brkrot/AlsHelper/Documents/צילומי מסך אפליקציה/מסך בחירת החיישנים.jpg

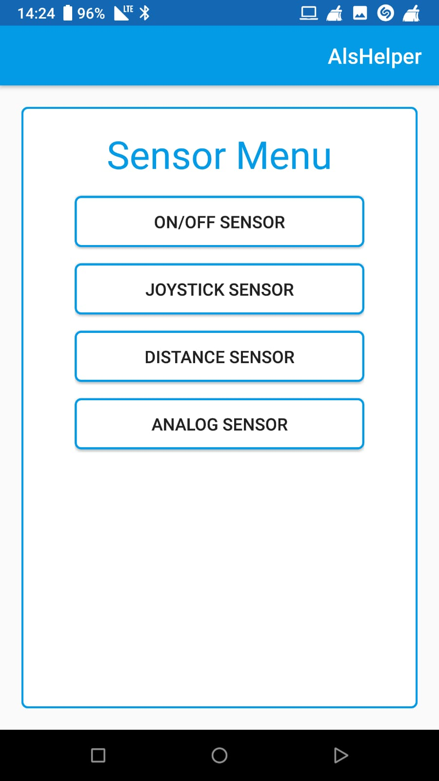
Documents/צילומי מסך אפליקציה/מסך בחירת החיישנים.jpg
