brkrot/AlsHelper/Documents/צילומי מסך אפליקציה/מסך שיתוף קוד אישי.jpg

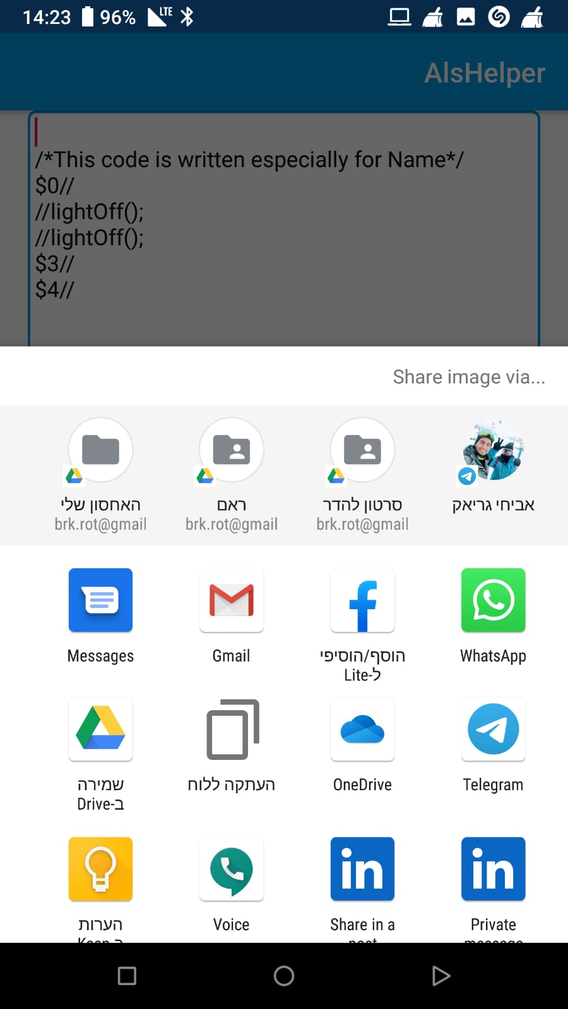
Documents/צילומי מסך אפליקציה/מסך שיתוף קוד אישי.jpg
