brkrot/AlsHelper/Documents/צילומי מסך אפליקציה/מסך תקשורת עזר 1.jpg

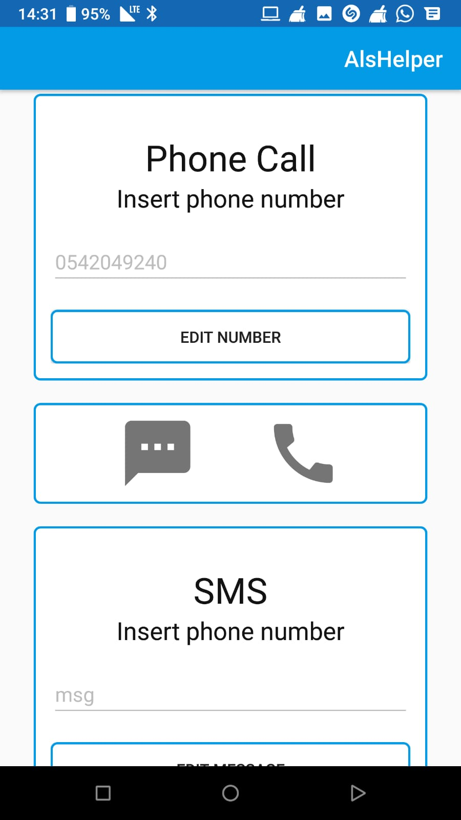
Documents/צילומי מסך אפליקציה/מסך תקשורת עזר 1.jpg
