brkrot/AlsHelper/Documents/צילומי מסך אפליקציה/מסך תקשורת עזר 2.jpg

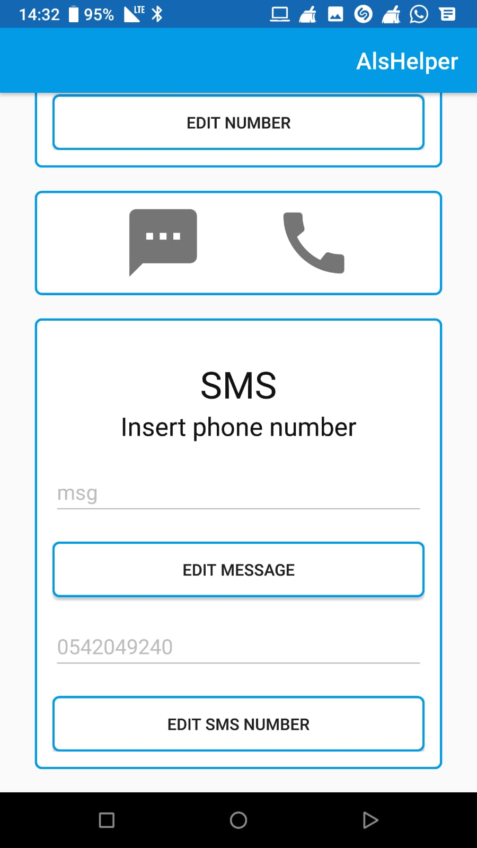
Documents/צילומי מסך אפליקציה/מסך תקשורת עזר 2.jpg
