brkrot/AlsHelper/Documents/צילומי מערכת/חיישן כפתור לחיצה רכה.jpeg

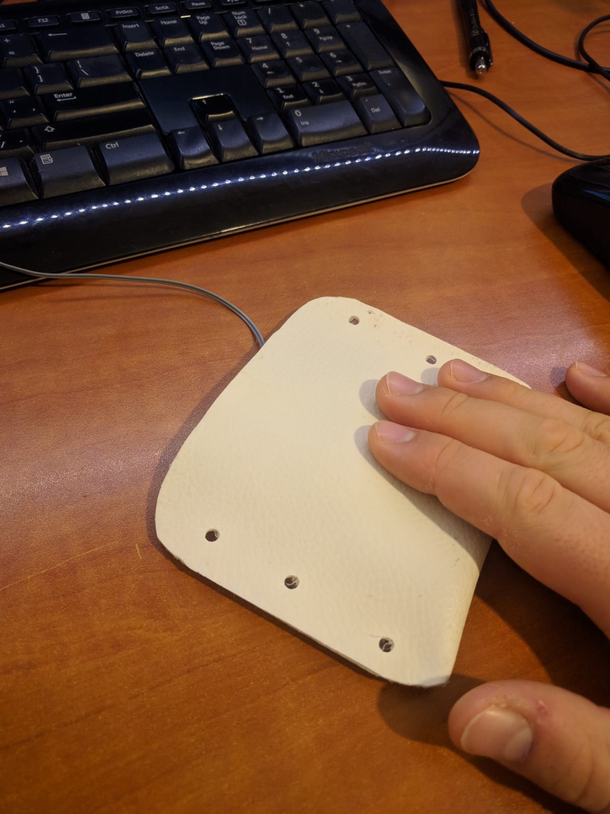
Documents/צילומי מערכת/חיישן כפתור לחיצה רכה.jpeg
