brkrot/AlsHelper/Documents/צילומי מערכת/מערכת עזר מבט חיצוני כולל.jpeg

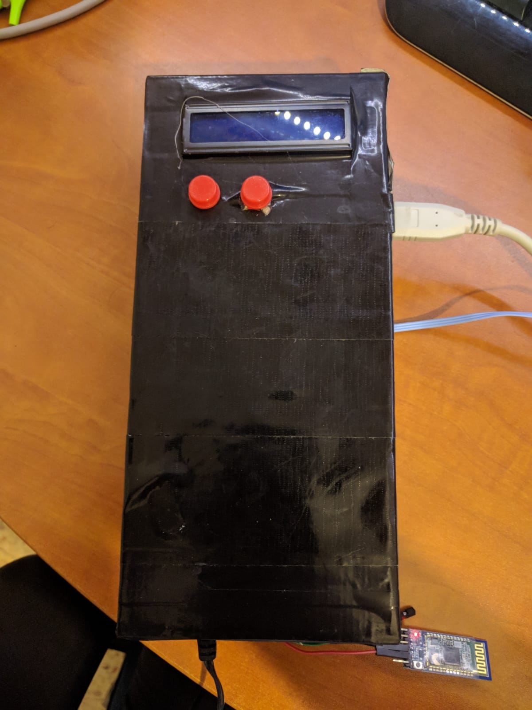
Documents/צילומי מערכת/מערכת עזר מבט חיצוני כולל.jpeg
