brkrot/AlsHelper/Documents/צילומי מערכת/מערכת עזר מבט חיצוני על המסך.jpeg

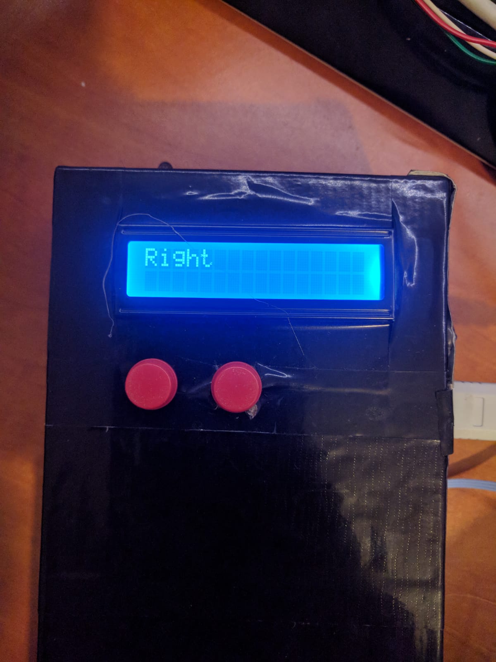
Documents/צילומי מערכת/מערכת עזר מבט חיצוני על המסך.jpeg
