brkrot/AlsHelper/Documents/צילומי מערכת/מערכת עזר פנימי.jpg

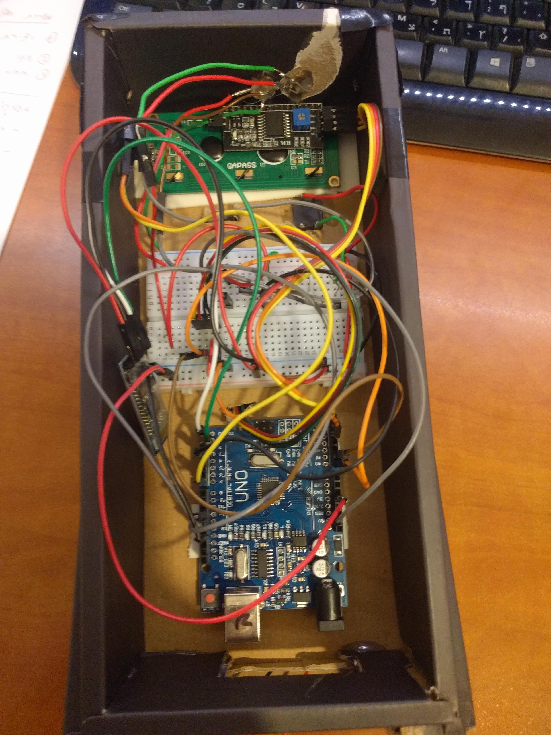
Documents/צילומי מערכת/מערכת עזר פנימי.jpg
