brkrot/AlsHelper/Documents/תרשימים/Helping_System_Sketch_2.0_bb.png

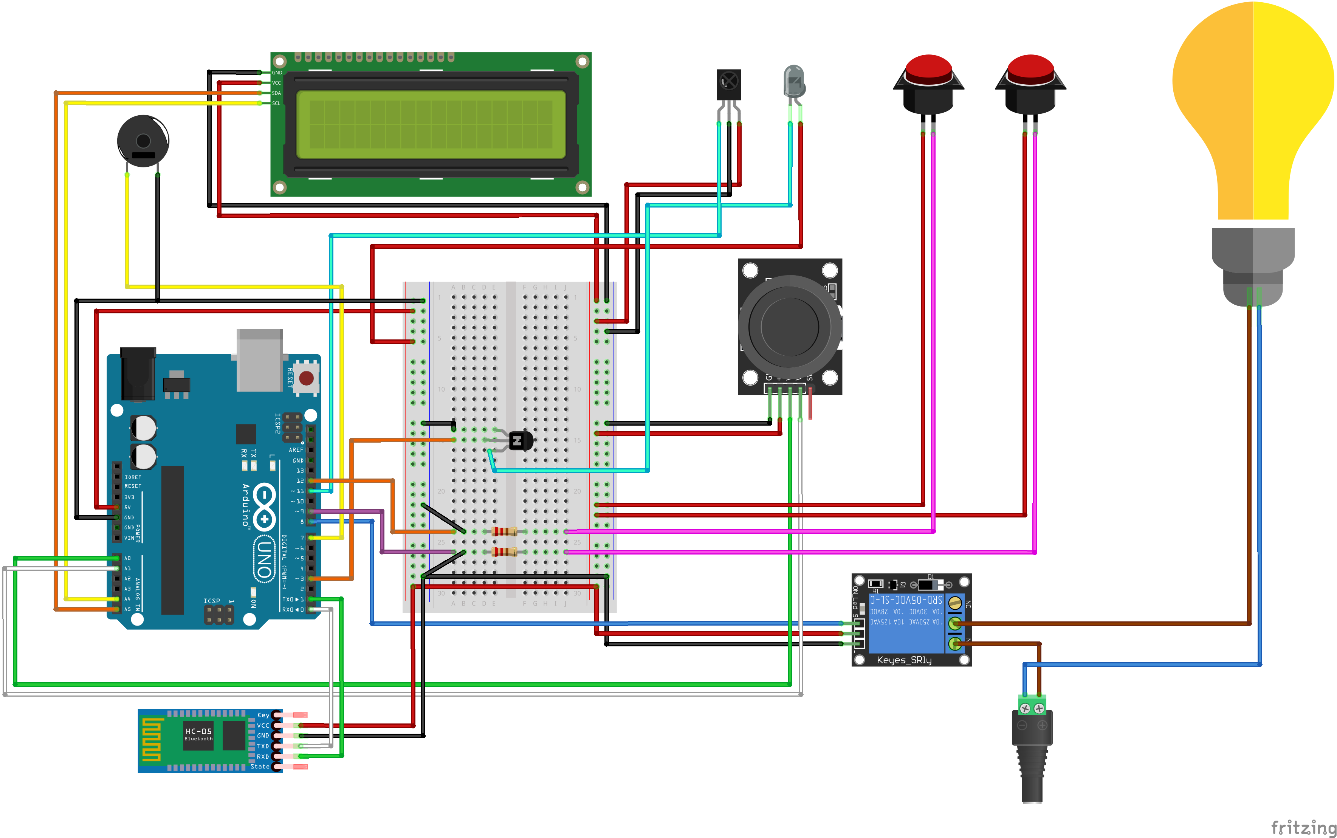
Documents/תרשימים/Helping_System_Sketch_2.0_bb.png
