brkrot/AlsHelper/Documents/תרשימים/IR_Reciever_Transmitter_Sketch_1.0_bb.png

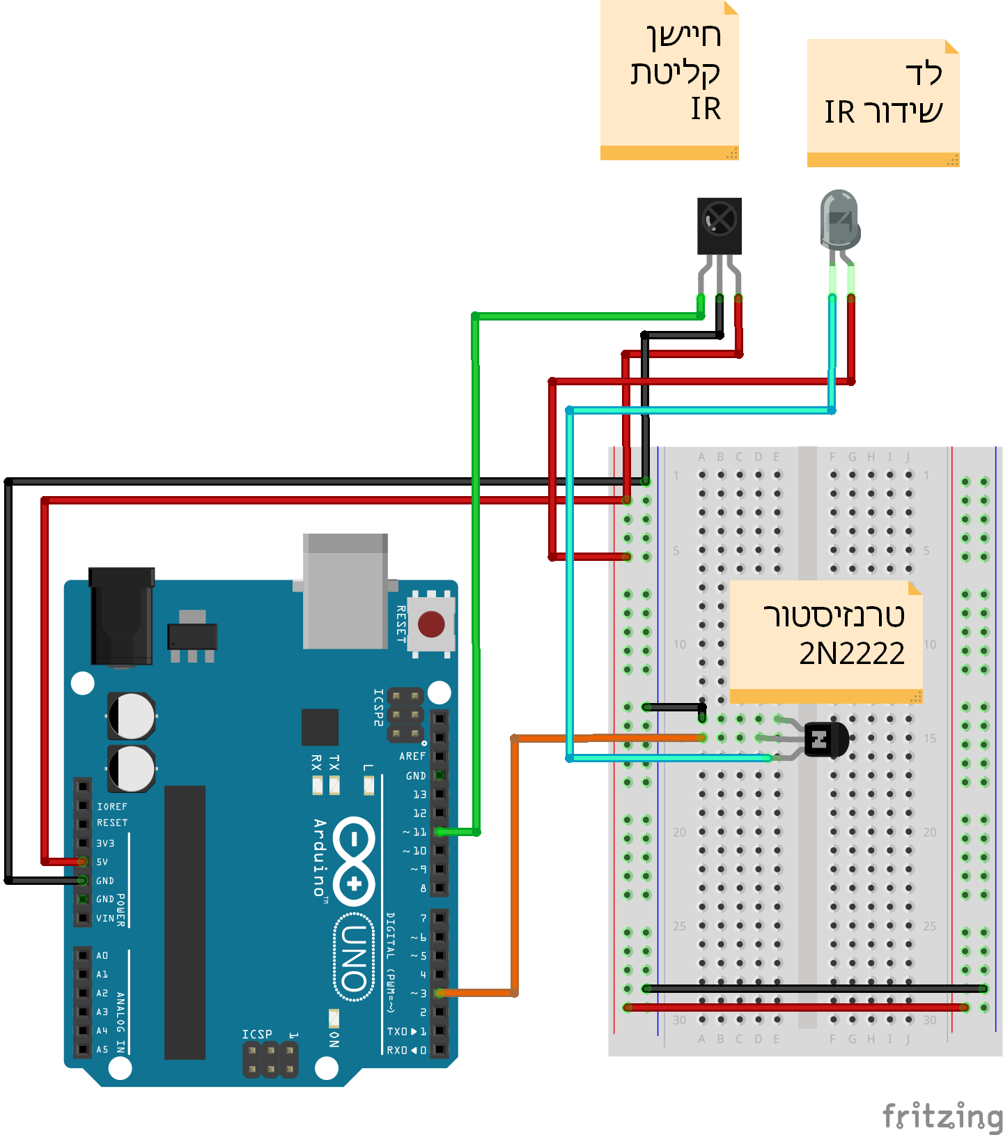
Documents/תרשימים/IR_Reciever_Transmitter_Sketch_1.0_bb.png
