brkrot/AlsHelper/Documents/תרשימים/תרשים מערכת ניתחו עם גויסטיק וצבעי חוטים.png

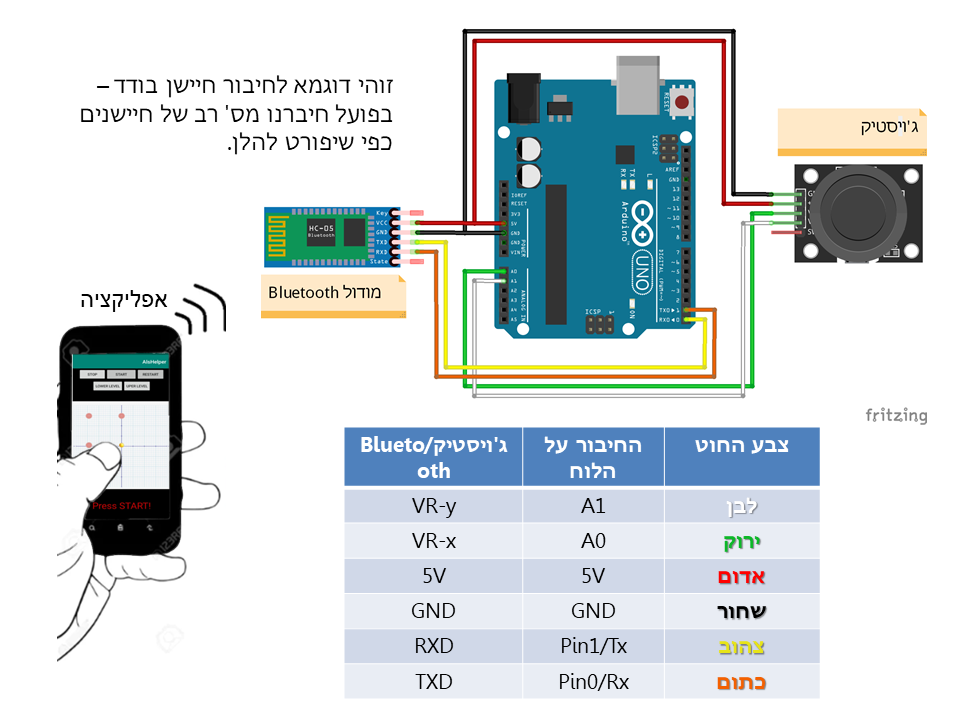
Documents/תרשימים/תרשים מערכת ניתחו עם גויסטיק וצבעי חוטים.png
